graysonlentner-pencil/ModelDesignPortfolio/2025-12-18-172731.png

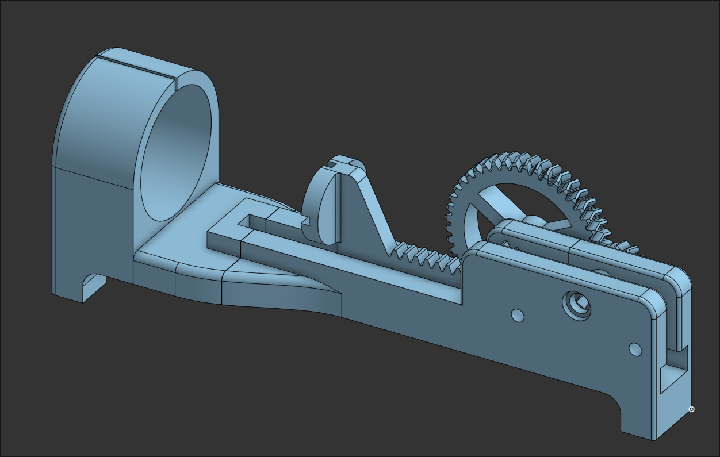
2025-12-18-172731.png
